inmbolmie/elfacun/images/B1.JPG

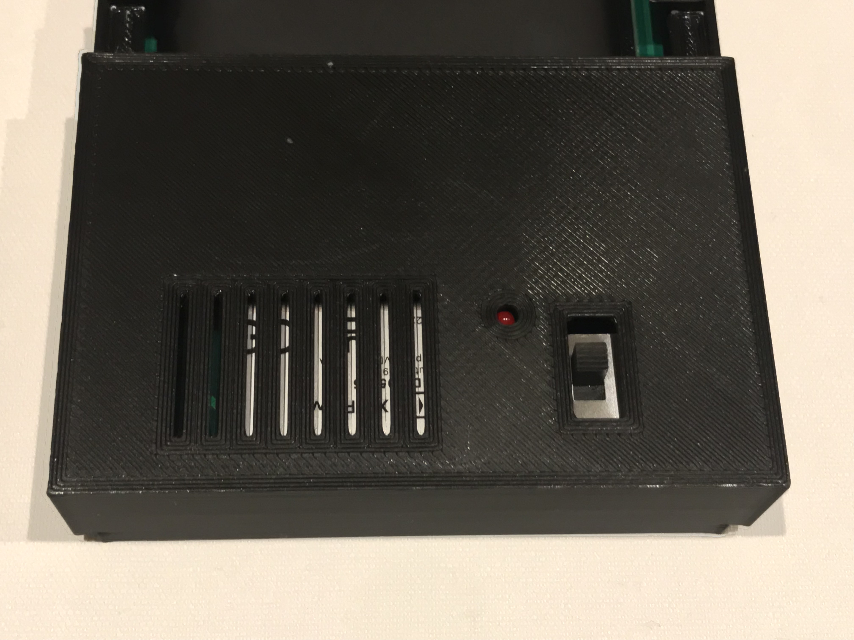
images/B1.JPG
