inmbolmie/elfacun/images/buttons.jpeg

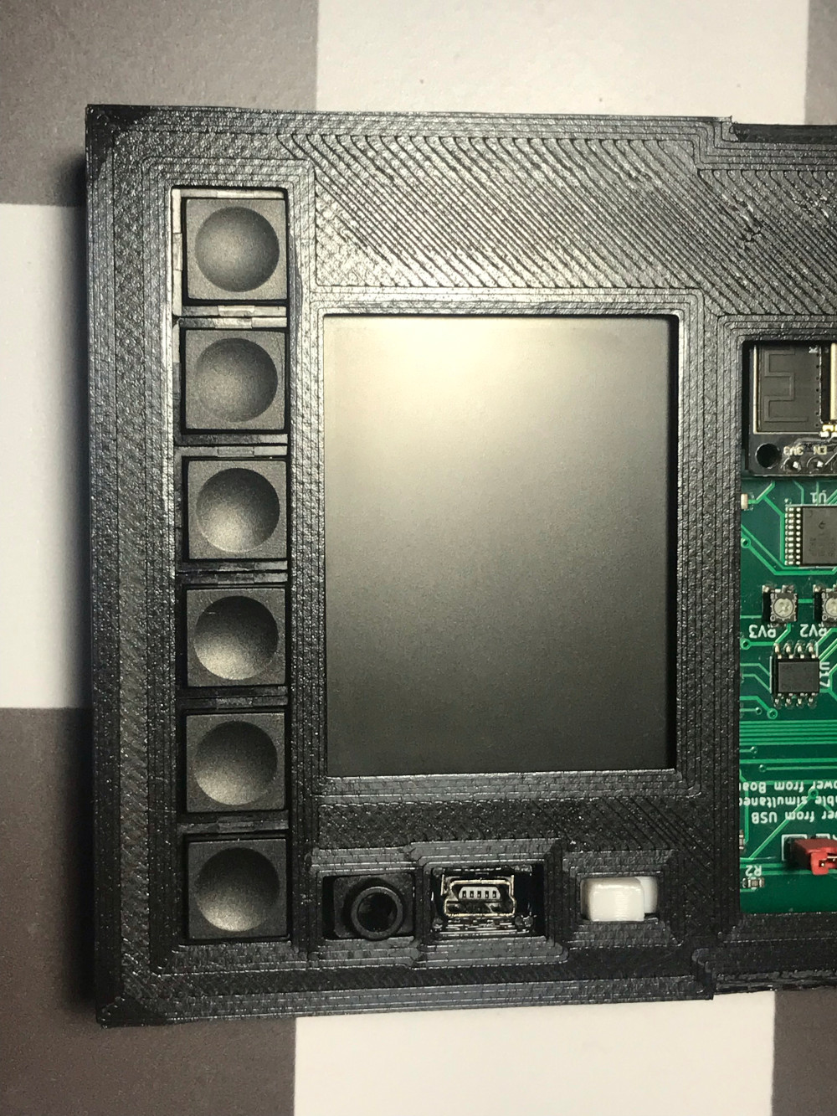
images/buttons.jpeg
