inmbolmie/elfacun/images/R6.jpg

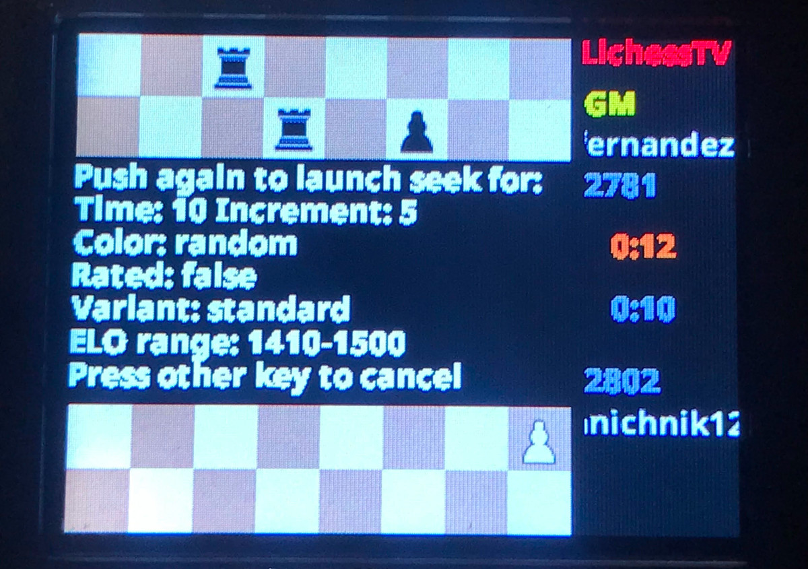
images/R6.jpg
