inmbolmie/elfacun/Kicad/v2.1/elfacun_v21.png

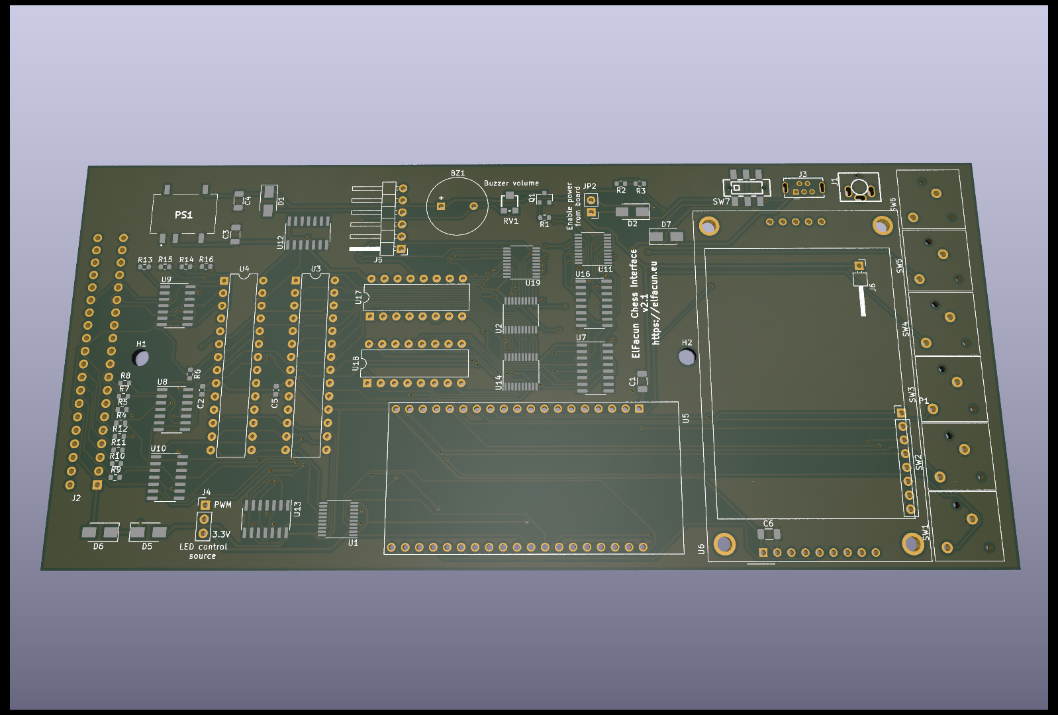
Kicad/v2.1/elfacun_v21.png
