inmbolmie/elfacun/pcb/v2.1/sample.png

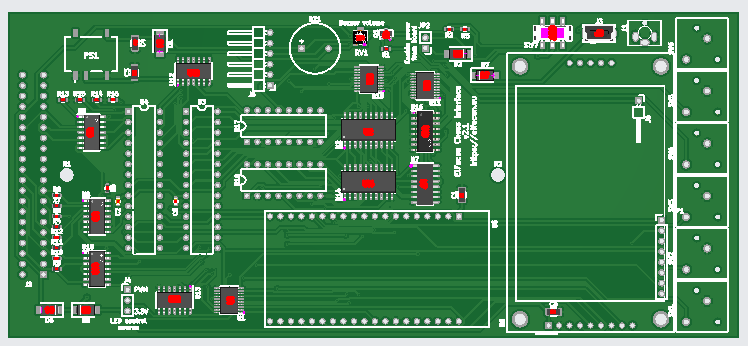
pcb/v2.1/sample.png
