inmbolmie/elfacun/elfacun/screen.cpp

/*
    ElFacun Chess Module software for ESP32
    © 2022 Inmbolmie inmbolmie [at] gmail [dot] com
    Distributed under the GNU GPL V3.0 license

    This program is distributed WITHOUT ANY WARRANTY, even the
    implied warranty of MERCHANTABILITY or FITNESS FOR A PARTICULAR
    PURPOSE.  See the GNU General Public License for more details.
*/

#include "screen.h"
#include "serial.h"
#include "i2c_clock.h"
#include "lichess.h"
#include "driver/ledc.h"

int lichessTopLastShownTime = 0;
int lichessBottomLastShownTime = 0;
boolean lichessBottomLastShownTimeToMove = false;
boolean lichessTopLastShownTimeToMove = false;
boolean centerBoardOnScreen = true;

char lichessConfirmationMsg[200];
boolean displayLichessConfirmationMsg = false;
boolean displayLichessSeekMsg = false;
const char*  lichessBottomNameActive;
const char*  lichessTopNameActive;
boolean signalResetTopPlayer = false;
boolean signalResetBottomPlayer = false;
int topPlayerTextSize = 0;
int bottomPlayerTextSize = 0;

int lastLedShownScreen = 64;

int lastRssiPainted = 0;

unsigned long lastLedShownScreenMillis = 0;

boolean doPaintBLEConnectedIcon = false;
boolean doPaintBLEConnectedIconDisabled = false;
boolean doClearBLEConnectedIcon = false;

boolean doPaintChess960ModeIcon = false;
boolean doClearChess960ModeIcon = false;

int toScrollTopPlayer = 0;
int toScrollBottomPlayer = 0;

byte currentTftBrightness = 255;

boolean isBrightnessAdjustmentDisabled = true;

SemaphoreHandle_t xScreenSemaphore;

const TickType_t screenSemaphoreTimeout = 5000 / portTICK_PERIOD_MS;

TFT_eSPI tft = TFT_eSPI();
TFT_eSprite spr = TFT_eSprite(&tft);
TFT_eSprite sprb = TFT_eSprite(&tft);


void initialize_tft() {
  tft.init();            // initialize LCD
  tft.setRotation(3);    //3-Landscape mode with SD card slot pointing backwards
  tft.setSwapBytes(true);
  tft.fillScreen(TFT_BLACK);
  tft.setCursor(0, 0);
  tft.setTextColor(TFT_WHITE); tft.setTextSize(1);

  //Semaphore to handle access to screen and SPI bus
  xScreenSemaphore = xSemaphoreCreateMutex();
  //unlocked by default
  xSemaphoreGive( ( xScreenSemaphore ) );

}




void paintBLEDebugUpdateMode() {

  //Called from displayBoard so no lock needed
  tft.fillRect(280, 220, 20, 20, TFT_BLACK);
  tft.setTextSize(1);
  tft.setTextWrap(false);

  tft.setCursor(280, 220);
  tft.setTextColor(TFT_WHITE);
  tft.printf("%d" , updateModeTypeBUSBBoard);

  return;
}



void paintBLEConnectedIcon() {
  //Called from displayBoard so no lock needed
  tft.fillRect(300, 220, 20, 20, TFT_BLACK);
  tft.setTextSize(1);
  tft.setTextWrap(false);

  tft.setCursor(300, 220);
  tft.setTextColor(TFT_WHITE);
  tft.printf("B");
  return;
}


void paintChess960ModeIcon() {
  //Called from displayBoard so no lock needed
  tft.fillRect(250, 220, 20, 20, TFT_BLACK);
  tft.setTextSize(1);
  tft.setTextWrap(false);

  tft.setCursor(250, 220);
  tft.setTextColor(TFT_WHITE);
  tft.printf("960");
  return;
}



void paintBLEConnectedIconDisabled() {

  //Called from displayBoard so no lock needed
  paintBLEConnectedIcon();
  tft.drawLine(298, 218, 313, 233, TFT_WHITE);
  tft.drawLine(313, 218, 298, 233, TFT_WHITE);

  return;
}

void paintBLEConnectedIconClear() {
  //Called from displayBoard so no lock needed

  tft.fillRect(298, 218, 20, 20, TFT_BLACK);
  return;
}

void paintChess960ModeIconClear() {
  //Called from displayBoard so no lock needed

  tft.fillRect(248, 218, 30, 20, TFT_BLACK);
  return;
}



void clearScreen() {
  xSemaphoreTake( xScreenSemaphore, ( TickType_t ) screenSemaphoreTimeout );
  tft.fillScreen(TFT_BLACK);
  if (BLEdeviceConnected) {
    paintBLEConnectedIcon();
  }
  if (chess960ModeEnabled) {
    paintChess960ModeIcon();
  }

  xSemaphoreGive( ( xScreenSemaphore ) );
}


void greyScreen() {
  xSemaphoreTake( xScreenSemaphore, ( TickType_t ) screenSemaphoreTimeout );
  tft.fillScreen(TFT_DARKGREY);
  if (BLEdeviceConnected) {
    paintBLEConnectedIcon();
  }
  if (chess960ModeEnabled) {
    paintChess960ModeIcon();
  }


  xSemaphoreGive( ( xScreenSemaphore ) );
}


void setDefaultTftBrightness() {
  currentTftBrightness = (uint8_t)atoi(screenBrightnessDefault);

  if (currentTftBrightness < 5) {
    currentTftBrightness = 64;
  }
  if (serialLog) Serial.print("Set default brightness: ");
  if (serialLog) Serial.println(currentTftBrightness, DEC);
  setTftBrightness(currentTftBrightness);
}

void setTftBrightness(byte brightness) {

  if (!isBrightnessAdjustmentDisabled) {

    if (serialLog) Serial.print("Set brightness: ");
    if (serialLog) Serial.println(brightness, DEC);
    //Set brightness on V2 hardware
    if (isV2Hardware) {
      ledcSetup(5, 800000, 8);
      ledcAttachPin(SCREEN_BRIGHTNESS, 5);
      ledcWrite(5, brightness);
    }
    currentTftBrightness = brightness;
  } else {

    if (serialLog) Serial.println("Set brightness MAX");
    pinMode(SCREEN_BRIGHTNESS, OUTPUT);
    digitalWrite(SCREEN_BRIGHTNESS, true);
  }

}


void increaseTftBrightness() {

  if (currentTftBrightness <= 252) {
    currentTftBrightness += 2;
  } else {
    currentTftBrightness = 255;
  }

  setTftBrightness(currentTftBrightness);
}


void decreaseTftBrightness() {

  if (currentTftBrightness >= 7) {
    currentTftBrightness -= 2;
  } else {
    currentTftBrightness = 5;
  }

  setTftBrightness(currentTftBrightness);

}


void storeAdjustedBrightness() {

  char cstr[4];
  sprintf(cstr, "%d", currentTftBrightness);
  storeNvsValue("screenbr", cstr);

}



// These read 16- and 32-bit types from the SD card file.
// BMP data is stored little-endian, Arduino is little-endian too.
// May need to reverse subscript order if porting elsewhere.

uint16_t read16(fs::File &f) {
  uint16_t result;
  ((uint8_t *)&result)[0] = f.read(); // LSB
  ((uint8_t *)&result)[1] = f.read(); // MSB
  return result;
}

uint32_t read32(fs::File &f) {
  uint32_t result;
  ((uint8_t *)&result)[0] = f.read(); // LSB
  ((uint8_t *)&result)[1] = f.read();
  ((uint8_t *)&result)[2] = f.read();
  ((uint8_t *)&result)[3] = f.read(); // MSB
  return result;
}


// Bodmers BMP image rendering function
// https://github.com/Bodmer/TFT_eSPI/blob/master/examples/Generic/TFT_SPIFFS_BMP/BMP_functions.ino
void drawBmp(const char *filename, int16_t x, int16_t y) {

  if ((x >= tft.width()) || (y >= tft.height())) return;

  fs::File bmpFS;

  // Open requested file on SD card
  bmpFS = SPIFFS.open(filename, "r");

  if (!bmpFS)
  {
    if (serialLog) Serial.print("File not found: ");
    if (serialLog) Serial.println(filename);
    return;
  }

  uint32_t seekOffset;
  uint16_t w, h, row, col;
  uint8_t  r, g, b;

  uint32_t startTime = millis();

  if (read16(bmpFS) == 0x4D42)
  {
    read32(bmpFS);
    read32(bmpFS);
    seekOffset = read32(bmpFS);
    read32(bmpFS);
    w = read32(bmpFS);
    h = read32(bmpFS);

    if ((read16(bmpFS) == 1) && (read16(bmpFS) == 24) && (read32(bmpFS) == 0))
    {
      y += h - 1;

      bool oldSwapBytes = tft.getSwapBytes();
      tft.setSwapBytes(true);
      bmpFS.seek(seekOffset);

      uint16_t padding = (4 - ((w * 3) & 3)) & 3;
      uint8_t lineBuffer[w * 3 + padding];

      for (row = 0; row < h; row++) {

        bmpFS.read(lineBuffer, sizeof(lineBuffer));
        uint8_t*  bptr = lineBuffer;
        uint16_t* tptr = (uint16_t*)lineBuffer;
        // Convert 24 to 16 bit colours
        for (uint16_t col = 0; col < w; col++)
        {
          b = *bptr++;
          g = *bptr++;
          r = *bptr++;
          *tptr++ = ((r & 0xF8) << 8) | ((g & 0xFC) << 3) | (b >> 3);
        }

        // Push the pixel row to screen, pushImage will crop the line if needed
        // y is decremented as the BMP image is drawn bottom up
        tft.pushImage(x, y--, w, 1, (uint16_t*)lineBuffer);
      }
      tft.setSwapBytes(oldSwapBytes);
      //if (serialLog) Serial.print("Loaded in ");
      //if (serialLog) Serial.print(millis() - startTime);
      //if (serialLog) Serial.println(" ms");
    }
    else if (serialLog) Serial.println("BMP format not recognized.");
  }
  bmpFS.close();
}


//
//void displayLichessConfirmationMessage() {
//
//  if (displayLichessConfirmationMsg) {
//    spr.pushSprite(0, 60);
//    if (serialLog) Serial.println("Push sprite------------------------------------>");
//  }
//}



const char hex[17] = "0123456789ABCDEF";

void displayBoard() {
  xSemaphoreTake( xScreenSemaphore, ( TickType_t ) screenSemaphoreTimeout );

  int boardOriginX = 0;
  int boardOriginY = 0;

  if ((isExternalClock || centerBoardOnScreen) && !isLichessConnected) {
    boardOriginX = 40;
    boardOriginY = 0;
  }

  tft.setTextSize(2);
  tft.setCursor(boardOriginX, boardOriginY);



  int square = 0;
  int visibleSquare = 0;
  int line = 0;
  int linepos = 0;

  int x = boardOriginX;
  int y = boardOriginY;

  if (!isExternalClock && refreshClock) {
    //Release temporarily to call display_clock()
    xSemaphoreGive( ( xScreenSemaphore ) );
    display_clock();
    xSemaphoreTake( xScreenSemaphore, ( TickType_t ) screenSemaphoreTimeout );
    send_clock();
    refreshClock = false;
  }

  boolean ledActivatedScreen = false;

  while (square < 64) {

    visibleSquare = square;

    byte bgcolor = 1;
    if ((line % 2) == (square % 2)) {
      bgcolor = 0;
    }

    x = boardOriginX + (square % 8) * 30;
    y = boardOriginY + line * 30;

    byte squareToShow = currentPos[visibleSquare];

    if (boardInverted) {
      squareToShow = currentPos[63 - visibleSquare];
    }

    if (isLichessConnected) {
      int index = visibleSquare;
      if (boardInverted) {
        index = 63 - visibleSquare;
      }
      squareToShow = lichessBoardPosition[index];
      if (lichessBoardPositionMarked[index] == 1) {
        bgcolor += 2;
      }

      //RSSI indicator
      if (measuredRssi != lastRssiPainted) {
        if (measuredRssi == 1) {
          tft.fillCircle(250, 230, 6, TFT_GREEN);
        }
        if (measuredRssi == 2) {
          tft.fillCircle(250, 230, 6, TFT_ORANGE);
        }
        if (measuredRssi == 3) {
          tft.fillCircle(250, 230, 6, TFT_RED);
        }
      }
    }

    if (isPassiveMode && !updateRemoteLedsAvailable()) {

      int index = visibleSquare;

      if ((lastLedShownScreenMillis + 500) < millis() ) {

        if (lastLedShownScreen == 64 || index > lastLedShownScreen ) {

          if (ledStatus[63 - index] && index != lastLedShownScreen && !ledActivatedScreen) {
            bgcolor += 2;
            lastLedShownScreen = index;
            lastLedShownScreenMillis = millis();
            ledActivatedScreen = true;
            buup();
          }
        }
      } else if (index == lastLedShownScreen) {
        bgcolor += 2;
        ledActivatedScreen = true;
      }
    }


    if ((lastDrawn[visibleSquare] != squareToShow || lastDrawnBG[visibleSquare] != bgcolor)  && ((displayLichessConfirmationMsg == false && displayLichessSeekMsg == false) || square <= 15 || square >= 48  )) {
      lastDrawn[visibleSquare] = squareToShow;
      lastDrawnBG[visibleSquare] = bgcolor;
      String pieceChar = String(squareToShow, HEX);
      pieceChar.toUpperCase();
      String filename = "/" + pieceChar + bgcolor + ".bmp";
      drawBmp(filename.c_str(), x, y);


    }

    square++;
    linepos++;
    if (linepos == 8) {
      linepos = 0;
      line++;
      tft.println("");
    }
  }


  if (!ledActivatedScreen) {
    lastLedShownScreen = 64;
  }

  //displayLichessConfirmationMessage();

  //paintBLEDebugUpdateMode();

  if (doPaintBLEConnectedIcon) {
    if (serialLog) Serial.println("Paint connected BLE");
    doPaintBLEConnectedIcon = false;
    paintBLEConnectedIcon();
  }

  if (doPaintBLEConnectedIconDisabled) {
    if (serialLog) Serial.println("Paint disabled BLE");
    doPaintBLEConnectedIconDisabled = false;
    paintBLEConnectedIconDisabled();
  }

  if (doClearBLEConnectedIcon) {
    if (serialLog) Serial.println("Clear BLE");
    doClearBLEConnectedIcon = false;
    paintBLEConnectedIconClear();
  }

  if (doPaintChess960ModeIcon) {
    if (serialLog) Serial.println("Paint 960");
    doPaintChess960ModeIcon = false;
    paintChess960ModeIcon();
  }


  if (doClearChess960ModeIcon) {
    if (serialLog) Serial.println("Clear 960");
    doClearChess960ModeIcon = false;
    paintChess960ModeIconClear();
  }


  xSemaphoreGive( ( xScreenSemaphore ) );


}






// http://javl.github.io/image2cpp/
// 'Scally', 107x180px
const uint16_t epd_bitmap_scally [] PROGMEM = {
  0x0000, 0x0000, 0x0000, 0x0000, 0x0000, 0x0000, 0x0000, 0x0000, 0x0000, 0x0000, 0x0000, 0x0000, 0x0000, 0x0000, 0x0000, 0x0000, 
  0x0000, 0x0000, 0x0000, 0x0000, 0x0000, 0x0000, 0x0000, 0x0000, 0x0000, 0x0000, 0x0000, 0x0000, 0x0000, 0x0000, 0x0000, 0x0000, 
  0x0000, 0x0000, 0x0000, 0x0000, 0x0000, 0x0000, 0x0000, 0x0000, 0x1082, 0x2104, 0x31a6, 0x4a69, 0x5acb, 0x6b6d, 0x7bcf, 0x7bcf, 
  0x7bcf, 0x7bcf, 0x7bcf, 0x7bcf, 0x7bcf, 0x73ae, 0x630c, 0x5acb, 0x52aa, 0x4208, 0x2965, 0x18c3, 0x0861, 0x0000, 0x0000, 0x0000, 
  0x0000, 0x0000, 0x0000, 0x0000, 0x0000, 0x0000, 0x0000, 0x0000, 0x0000, 0x0000, 0x0000, 0x0000, 0x0000, 0x0000, 0x0000, 0x0000, 
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
  0x9492, 0x9cd3, 0x9cf3, 0x9cf3, 0x9cf3, 0x9cf3, 0x9cf3, 0x9cf3, 0x9cf3, 0x9cd3, 0x94b2, 0x9492, 0x9492, 0x9492, 0x94b2, 0x94b2, 
  0x94b2, 0x94b2, 0x94b2, 0x9492, 0x9492, 0x9492, 0x94b2, 0x9492, 0x94b2, 0x94b2, 0x94b2, 0x8c71, 0x8410, 0x632c, 0x39c7, 0x0841, 
  0x0000, 0x0000, 0x0000, 0x0000, 0x0000, 0x0000, 0x0000, 0x0000, 0x0000, 0x0000, 0x0000, 0x0000, 0x0000, 0x0000, 0x0000, 0x0000, 
  0x0000, 0x0000, 0x0000, 0x0000, 0x0000, 0x0000, 0x0000, 0x0000, 0x0000, 0x0000, 0x0000, 0x0000, 0x0000, 0x0000, 0x0000, 0x0000, 
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
};




void displayScallyHomage() {

  if (strcmp(scallyHomage, "TRUE") == 0) {
    
    tft.pushImage(106, 10, 107, 180, epd_bitmap_scally);
    tft.setTextSize(1);
    tft.setCursor(60, 210);
    tft.setTextColor(TFT_DARKGREY);
    tft.print("In memoriam Alan 'Scally' Cooper");
    tft.setCursor(130, 225);
    tft.print("1956-2024");
    delay(1500);
  }
  
}


void displayLichessLogo() {
  xSemaphoreTake( xScreenSemaphore, ( TickType_t ) screenSemaphoreTimeout );
  if (serialLog) Serial.println("Displaying Lichess logo");
  tft.fillScreen(TFT_BLACK);
  displayScallyHomage();
  tft.fillScreen(TFT_BLACK);
  drawBmp("/lich.bmp", 110, 70);
  xSemaphoreGive( ( xScreenSemaphore ) );
}


void displayModeALogo() {
  xSemaphoreTake( xScreenSemaphore, ( TickType_t ) screenSemaphoreTimeout );
  if (serialLog) Serial.println("Displaying Mode A logo");
  tft.fillScreen(TFT_BLACK);
  displayScallyHomage();
  tft.fillScreen(TFT_BLACK);
  drawBmp("/modea.bmp", 110, 100);
  xSemaphoreGive( ( xScreenSemaphore ) );
}


void displayModeBLogo() {
  xSemaphoreTake( xScreenSemaphore, ( TickType_t ) screenSemaphoreTimeout );
  if (serialLog) Serial.println("Displaying Mode B logo");
  tft.fillScreen(TFT_BLACK);
  displayScallyHomage();
  tft.fillScreen(TFT_BLACK);
  drawBmp("/modeb.bmp", 110, 100);
  xSemaphoreGive( ( xScreenSemaphore ) );
}

//http://javl.github.io/image2cpp/
const uint16_t epd_bitmap_modec [] PROGMEM = {
  0x0000, 0x0000, 0x0000, 0x0000, 0x0000, 0x0000, 0x0000, 0x0000, 0x0000, 0x0000, 0x0000, 0x0000, 0x0000, 0x0000, 0x0000, 0x0000,
  0x0000, 0x0000, 0x0000, 0x0000, 0x0000, 0x0000, 0x0000, 0x0000, 0x0000, 0x0000, 0x0000, 0x0000, 0x0000, 0x0000, 0x0000, 0x0000,
  0x0000, 0x0000, 0x0000, 0x0000, 0x0000, 0x0000, 0x0000, 0x0000, 0x0000, 0x0000, 0x0000, 0x0000, 0x0000, 0x0000, 0x0000, 0x0000,
  0x0000, 0x0000, 0x0000, 0x0000, 0x0000, 0x0000, 0x0000, 0x0000, 0x0000, 0x0000, 0x0000, 0x0000, 0x0000, 0x0000, 0x0000, 0x0000,
  0x0000, 0x0000, 0x0000, 0x0000, 0x0000, 0x0000, 0x0000, 0x0000, 0x0000, 0x0000, 0x0000, 0x0000, 0x0000, 0x0000, 0x0000, 0x0000,
  0x0000, 0x0000, 0x0000, 0x0000, 0x0000, 0x0000, 0x0000, 0x0000, 0x39c7, 0xffdf, 0xffdf, 0xffdf, 0xd6ba, 0x0000, 0x0000, 0x0000,
  0x0000, 0x0000, 0x0000, 0x0000, 0x18e3, 0xef5d, 0xffdf, 0xffdf, 0xf7be, 0x10a2, 0x0000, 0x0000, 0x0000, 0x0000, 0x0000, 0x0000,
  0x0000, 0x0000, 0x0000, 0x0000, 0x0000, 0x0000, 0x0000, 0x0000, 0x0000, 0x0000, 0x0000, 0x0000, 0x0000, 0x0000, 0x0000, 0x0000,
  0x0000, 0x0000, 0x0000, 0x0000, 0x0000, 0x0000, 0xf79e, 0xffdf, 0x8430, 0x0000, 0x0000, 0x0000, 0x0000, 0x0000, 0x0000, 0x0000,
  0x0000, 0x0000, 0x0000, 0x0000, 0x0000, 0x0000, 0x0000, 0x0000, 0x0000, 0x0000, 0x0000, 0x0000, 0x0000, 0x10a2, 0x9492, 0xce59,
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
  //drawBmp("/modec.bmp", 118, 110);
  xSemaphoreGive( ( xScreenSemaphore ) );
}





void clear_message() {
  xSemaphoreTake( xScreenSemaphore, ( TickType_t ) screenSemaphoreTimeout );
  tft.fillRect(245, 110, 75, 30, TFT_BLACK);
  xSemaphoreGive( ( xScreenSemaphore ) );
}


void display_message(String message) {
  xSemaphoreTake( xScreenSemaphore, ( TickType_t ) screenSemaphoreTimeout );
  tft.fillRect(245, 115, 75, 30, TFT_BLACK);
  tft.setCursor(245, 115);
  tft.setTextColor(TFT_WHITE);
  tft.println(message);
  xSemaphoreGive( ( xScreenSemaphore ) );

}


void display_clock() {
  xSemaphoreTake( xScreenSemaphore, ( TickType_t ) screenSemaphoreTimeout );


  if (!boardInverted) {

    tft.fillRect(245, 30, 75, 50, TFT_BLACK);
    tft.setCursor(255, 50);
    tft.setTextColor(TFT_WHITE);
    tft.printf("%01d", rhours);
    tft.print(":");
    tft.printf("%02d", rmins);
    tft.print(".");
    tft.printf("%02d", rsecs);

    tft.fillRect(245, 180, 75, 30, TFT_BLACK);
    tft.setCursor(255, 180);
    tft.printf("%01d", lhours);
    tft.print(":");
    tft.printf("%02d", lmins);
    tft.print(".");
    tft.printf("%02d", lsecs);
  } else {

    tft.fillRect(245, 30, 75, 50, TFT_BLACK);
    tft.setCursor(255, 50);
    tft.setTextColor(TFT_WHITE);
    tft.printf("%01d", lhours);
    tft.print(":");
    tft.printf("%02d", lmins);
    tft.print(".");
    tft.printf("%02d", lsecs);

    tft.fillRect(245, 180, 75, 30, TFT_BLACK);
    tft.setCursor(255, 180);
    tft.printf("%01d", rhours);
    tft.print(":");
    tft.printf("%02d", rmins);
    tft.print(".");
    tft.printf("%02d", rsecs);
  }

  xSemaphoreGive( ( xScreenSemaphore ) );
}



void paintLichessPlayerTopSprite(const char* lichessTopTitle, const char*  lichessTopName, long  lichessTopRating) {
  xSemaphoreTake( xScreenSemaphore, ( TickType_t ) screenSemaphoreTimeout );

  tft.fillRect(240, 0, 80, 80, TFT_BLACK);
  tft.setTextSize(1);
  tft.setTextWrap(false);

  if (isLichessConnected && !isLichessGameActive()) {
    tft.setCursor(245, 0);
    tft.setTextColor(TFT_RED);
    tft.printf("LichessTV");
  }

  tft.setCursor(247, 25);
  tft.setTextColor(TFT_ORANGE);
  tft.printf("%s", lichessTopTitle);


  //tft.setCursor(247, 45);
  //tft.setTextColor(TFT_WHITE);
  //tft.printf("%s", lichessTopName);


  if (lichessTopRating != NULL) {
    tft.setCursor(247, 65);
    tft.setTextColor(TFT_DARKGREY);
    tft.printf("%d", lichessTopRating);
  }



  spr.setColorDepth(8);
  spr.deleteSprite();
  spr.loadFont("NotoSansBold15"); // Must load the font first into the sprite class
  topPlayerTextSize = spr.textWidth(lichessTopName) + 7;
  spr.createSprite(topPlayerTextSize, 17);
  //spr.fillSprite(TFT_RED);

  spr.setTextColor(TFT_WHITE, TFT_BLACK); // Set the sprite font colour and the background colour
  //tft.setCursor(247, 45);
  //spr.setScrollRect(0, 0, 10 * strlen(lichessTopName), 17, TFT_BLACK);
  spr.printToSprite(lichessTopName);    // Prints to tft cursor position, tft cursor NOT moved

  spr.unloadFont(); // Remove the font from sprite class to recover memory used
  tft.fillRect(247, 45, 80, 20, TFT_BLACK);
  spr.pushSprite(247, 45);
  if (serialLog) Serial.print("Sprite TOP width----------------------> ");
  if (serialLog) Serial.println(topPlayerTextSize, DEC);


  toScrollTopPlayer = topPlayerTextSize + 60;
  delete lichessTopNameActive;
  lichessTopNameActive = strdup(lichessTopName);

  signalResetTopPlayer = false;

  xSemaphoreGive( ( xScreenSemaphore ) );
  return;

}


void refreshLichessPlayerTopSprite() {
  xSemaphoreTake( xScreenSemaphore, ( TickType_t ) screenSemaphoreTimeout );

  if (spr.width() > 0) {

    toScrollTopPlayer--;

    if ((toScrollTopPlayer >= 80) && (toScrollTopPlayer <= topPlayerTextSize) ) {
      spr.scroll(-1);
      spr.pushSprite(247, 45);
    }

    if (toScrollTopPlayer < 20) {
      signalResetTopPlayer = true;
    }

    if (toScrollTopPlayer < 20 && signalResetBottomPlayer) {
      signalResetBottomPlayer = false;
      spr.deleteSprite();
      spr.createSprite(topPlayerTextSize, 17);
      spr.loadFont("NotoSansBold15");
      //tft.fillRect(247, 45, 80, 20, TFT_BLACK);
      spr.fillSprite(TFT_BLACK);
      tft.setCursor(247, 45);
      spr.printToSprite(lichessTopNameActive);
      toScrollTopPlayer = topPlayerTextSize + 60;
      spr.unloadFont();
      spr.pushSprite(247, 45);

    }
  }

  xSemaphoreGive( ( xScreenSemaphore ) );
}



void paintLichessPlayerBottomSprite(const char* lichessBottomTitle, const char*  lichessBottomName, long  lichessBottomRating) {
  xSemaphoreTake( xScreenSemaphore, ( TickType_t ) screenSemaphoreTimeout );


  tft.fillRect(240, 120, 80, 80, TFT_BLACK);
  tft.setTextSize(1);
  tft.setTextWrap(false);

  if (lichessBottomRating != NULL) {
    tft.setCursor(247, 160);
    tft.setTextColor(TFT_DARKGREY);
    tft.printf("%d", lichessBottomRating);
  }

  //tft.setCursor(247, 180);
  //tft.setTextColor(TFT_WHITE);
  //tft.printf("%s", lichessBottomName);


  tft.setCursor(247, 200);
  tft.setTextColor(TFT_ORANGE);
  tft.printf("%s", lichessBottomTitle);


  sprb.setColorDepth(8);
  sprb.deleteSprite();
  sprb.loadFont("NotoSansBold15"); // Must load the font first into the sprite class
  bottomPlayerTextSize = sprb.textWidth(lichessBottomName) + 7;
  sprb.createSprite(bottomPlayerTextSize, 17);
  //spr.fillSprite(TFT_RED);

  sprb.setTextColor(TFT_WHITE, TFT_BLACK); // Set the sprite font colour and the background colour
  //tft.setCursor(247, 45);
  //spr.setScrollRect(0, 0, 10 * strlen(lichessTopName), 17, TFT_BLACK);
  sprb.printToSprite(lichessBottomName);    // Prints to tft cursor position, tft cursor NOT moved

  sprb.unloadFont(); // Remove the font from sprite class to recover memory used
  tft.fillRect(247, 180, 80, 20, TFT_BLACK);
  sprb.pushSprite(247, 180);

  if (serialLog) Serial.print("Sprite BOTTOM width----------------------> ");
  if (serialLog) Serial.println(bottomPlayerTextSize, DEC);

  toScrollBottomPlayer = bottomPlayerTextSize + 60;
  delete lichessBottomNameActive;
  lichessBottomNameActive = strdup(lichessBottomName);

  signalResetBottomPlayer = false;

  xSemaphoreGive( ( xScreenSemaphore ) );
  return;
}



void refreshLichessPlayerBottomSprite() {
  xSemaphoreTake( xScreenSemaphore, ( TickType_t ) screenSemaphoreTimeout );

  if (sprb.width() > 0) {

    toScrollBottomPlayer--;

    if ((toScrollBottomPlayer >= 80) && (toScrollBottomPlayer <= bottomPlayerTextSize )) {
      sprb.scroll(-1);
      sprb.pushSprite(247, 180);
    }

    if (toScrollBottomPlayer < 20) {
      signalResetBottomPlayer = true;
    }

    if (toScrollBottomPlayer < 20 && signalResetTopPlayer) {
      signalResetTopPlayer = false;
      sprb.deleteSprite();
      sprb.createSprite(bottomPlayerTextSize, 17);
      sprb.loadFont("NotoSansBold15");
      //tft.fillRect(247, 180, 80, 20, TFT_BLACK);
      sprb.fillSprite(TFT_BLACK);
      tft.setCursor(247, 180);
      sprb.printToSprite(lichessBottomNameActive);
      toScrollBottomPlayer = bottomPlayerTextSize + 60;
      sprb.unloadFont();
      sprb.pushSprite(247, 180);

    }
  }

  xSemaphoreGive( ( xScreenSemaphore ) );
}




void paintLichessPlayerTop(const char* lichessTopTitle, const char*  lichessTopName, long  lichessTopRating) {
  xSemaphoreTake( xScreenSemaphore, ( TickType_t ) screenSemaphoreTimeout );

  tft.fillRect(240, 0, 80, 80, TFT_BLACK);
  tft.setTextSize(1);
  tft.setTextWrap(false);

  if (isLichessConnected && !isLichessGameActive()) {
    tft.setCursor(245, 0);
    tft.setTextColor(TFT_RED);
    tft.printf("LichessTV");
  }

  tft.setCursor(247, 25);
  tft.setTextColor(TFT_ORANGE);
  tft.printf("%s", lichessTopTitle);


  tft.setCursor(247, 45);
  tft.setTextColor(TFT_WHITE);
  tft.printf("%s", lichessTopName);


  if (lichessTopRating != NULL) {
    tft.setCursor(247, 65);
    tft.setTextColor(TFT_DARKGREY);
    tft.printf("%d", lichessTopRating);
  }

  xSemaphoreGive( ( xScreenSemaphore ) );

  return;
}

void paintLichessPlayerBottom(const char* lichessBottomTitle, const char*  lichessBottomName, long  lichessBottomRating) {
  xSemaphoreTake( xScreenSemaphore, ( TickType_t ) screenSemaphoreTimeout );


  tft.fillRect(240, 120, 80, 80, TFT_BLACK);
  tft.setTextSize(1);
  tft.setTextWrap(false);

  if (lichessBottomRating != NULL) {
    tft.setCursor(247, 160);
    tft.setTextColor(TFT_DARKGREY);
    tft.printf("%d", lichessBottomRating);
  }

  tft.setCursor(247, 180);
  tft.setTextColor(TFT_WHITE);
  tft.printf("%s", lichessBottomName);


  tft.setCursor(247, 200);
  tft.setTextColor(TFT_ORANGE);
  tft.printf("%s", lichessBottomTitle);


  xSemaphoreGive( ( xScreenSemaphore ) );
  return;
}

void paintLichessPlayerClear() {
  xSemaphoreTake( xScreenSemaphore, ( TickType_t ) screenSemaphoreTimeout );
  tft.fillRect(240, 0, 80, 240, TFT_BLACK);
  lichessTopLastShownTime = 0;
  lichessBottomLastShownTime = 0;
  xSemaphoreGive( ( xScreenSemaphore ) );
  return;
}

void paintLichessTimeTop(long lichessTopTime, boolean isTimeToMove) {
  xSemaphoreTake( xScreenSemaphore, ( TickType_t ) screenSemaphoreTimeout );


  if (lichessTopTime != NULL) {

    if (lichessTopTime / 1000 == lichessTopLastShownTime && isTimeToMove == lichessTopLastShownTimeToMove) {
      xSemaphoreGive( ( xScreenSemaphore ) );
      return;
    }

    lichessTopLastShownTime = lichessTopTime / 1000;
    lichessTopLastShownTimeToMove = isTimeToMove;

    long minutes = lichessTopTime / 60000;
    long seconds = (lichessTopTime / 1000) % 60;

    tft.fillRect(247, 95, 80, 20, TFT_BLACK);

    tft.setCursor(260, 95);
    if (!isTimeToMove) {
      tft.setTextColor(TFT_DARKGREY);
    } else {
      tft.setTextColor(0xFA80);
    }
    tft.printf("%d:%02d", minutes, seconds);
  }
  xSemaphoreGive( ( xScreenSemaphore ) );
  return;
}

void paintLichessTimeBottom(long lichessBottomTime, boolean isTimeToMove) {
  xSemaphoreTake( xScreenSemaphore, ( TickType_t ) screenSemaphoreTimeout );
  if (lichessBottomTime != NULL) {

    if (lichessBottomTime / 1000 == lichessBottomLastShownTime && isTimeToMove == lichessBottomLastShownTimeToMove) {
      xSemaphoreGive( ( xScreenSemaphore ) );
      return;
    }

    lichessBottomLastShownTime = lichessBottomTime / 1000;
    lichessBottomLastShownTimeToMove = isTimeToMove;

    long minutes = lichessBottomTime / 60000;
    long seconds = (lichessBottomTime / 1000) % 60;

    tft.fillRect(247, 125, 80, 20, TFT_BLACK);

    tft.setCursor(260, 125);
    if (!isTimeToMove) {
      tft.setTextColor(TFT_DARKGREY);
    } else {
      tft.setTextColor(0xFA80);
    }
    tft.printf("%d:%02d", minutes, seconds);
  }
  xSemaphoreGive( ( xScreenSemaphore ) );
  return;

}


void askForLichessConfirmation(const char* lichessTime, const char* lichessIncrement, const char* lichessRated, const char* lichessColor, const char* lichessElo) {

  //Called from the button read code so the semaphore is already taken

  displayLichessConfirmationMsg = true;

  //spr.setColorDepth(8);
  //spr.createSprite(240, 120);
  //spr.fillSprite(TFT_RED);
  //spr.loadFont("NotoSansBold15"); // Must load the font first into the sprite class
  //spr.setTextColor(TFT_WHITE, TFT_BLACK); // Set the sprite font colour and the background colour
  //tft.setCursor(0,0);
  //spr.setScrollRect(0, 0, 200, 80, TFT_YELLOW);
  //spr.printToSprite(lichessConfirmationMsg);    // Prints to tft cursor position, tft cursor NOT moved
  //spr.unloadFont(); // Remove the font from sprite class to recover memory used

  tft.fillRect(0, 60, 240, 120, TFT_BLACK);
  tft.setCursor(0, 63);
  tft.setTextColor(TFT_WHITE);
  if (strcmp(lichessElo, "NONE") == 0 || strcmp(lichessElo, "") == 0) {
    tft.printf("Push again to launch seek for:\nTime: %s Increment: %s\nColor: %s\nRated: %s\nVariant: standard\n\nPress other key to cancel", lichessTime, lichessIncrement, lichessColor, lichessRated );
  } else {
    tft.printf("Push again to launch seek for:\nTime: %s Increment: %s\nColor: %s\nRated: %s\nVariant: standard\nELO range: %s\nPress other key to cancel", lichessTime, lichessIncrement, lichessColor, lichessRated, lichessElo );
  }

}



void askForLichessConfirmationTakeBackOffer() {

  //Called from the button read code so the semaphore is already taken

  displayLichessConfirmationMsg = true;

  tft.fillRect(0, 60, 240, 120, TFT_BLACK);
  tft.setCursor(0, 83);
  tft.setTextColor(TFT_WHITE);
  tft.println(" Press again to ask takeback");
  tft.println("");
  tft.println(" Push any other button to abort");

}



void announceHoldMode() {

  //Called from the button read code so the semaphore is already taken

  displayLichessConfirmationMsg = true;

  tft.fillRect(0, 60, 240, 120, TFT_BLACK);
  tft.setCursor(0, 83);
  tft.setTextColor(TFT_WHITE);
  tft.println(" HOLD MODE");
  tft.println(" You can unplug the module");
  tft.println(" or turn it off safely");
  tft.println(" Push any key to release");


}


void announceLoadingResources() {


  tft.fillRect(0, 60, 320, 120, TFT_BLACK);
  tft.setCursor(0, 83);
  tft.setTextColor(TFT_WHITE);
  tft.setTextSize(2);
  tft.println(" UPDATING RESOURCES");
  tft.println(" Please do not turn off");
  tft.println(" the module. It can take");
  tft.println(" up to a minute");

}



void askForLichessConfirmationDrawOffer() {

  //Called from the button read code so the semaphore is already taken

  displayLichessConfirmationMsg = true;

  tft.fillRect(0, 60, 240, 120, TFT_BLACK);
  tft.setCursor(0, 83);
  tft.setTextColor(TFT_WHITE);
  tft.println(" Press again to offer draw");
  tft.println("");
  tft.println(" Push any other button to abort");

}

void askForLichessConfirmationResign() {

  //Called from the button read code so the semaphore is already taken

  displayLichessConfirmationMsg = true;

  tft.fillRect(0, 60, 240, 120, TFT_BLACK);
  tft.setCursor(0, 83);
  tft.setTextColor(TFT_WHITE);
  tft.println(" Press again to resign");
  tft.println("");
  tft.println(" Push any other button to abort");


}


void askForLichessConfirmationOpponentDrawOffer() {

  xSemaphoreTake( xScreenSemaphore, ( TickType_t ) screenSemaphoreTimeout );

  displayLichessConfirmationMsg = true;

  tft.fillRect(0, 60, 240, 120, TFT_BLACK);
  tft.setCursor(0, 83);
  tft.setTextColor(TFT_WHITE);
  tft.println(" Opponent offered a draw");
  tft.println("");
  tft.println(" Push first button to accept");
  tft.println("");
  tft.println(" Any other to decline");
  xSemaphoreGive( ( xScreenSemaphore ) );

}


void askForLichessConfirmationOpponentTakebackProposal() {

  xSemaphoreTake( xScreenSemaphore, ( TickType_t ) screenSemaphoreTimeout );

  displayLichessConfirmationMsg = true;

  tft.fillRect(0, 60, 240, 120, TFT_BLACK);
  tft.setCursor(0, 83);
  tft.setTextColor(TFT_WHITE);
  tft.println(" Opponent ask taking back");
  tft.println("");
  tft.println(" Push first button to accept");
  tft.println("");
  tft.println(" Any other to decline");

  xSemaphoreGive( ( xScreenSemaphore ) );
}




void cancelLichessConfirmation() {
  if (displayLichessConfirmationMsg) {
    displayLichessConfirmationMsg = false;
    memset(lastDrawn, 255, 64);
    memset(lastDrawnBG, 255, 64);
  }


}

void cancelLichessSeekScreen() {
  displayLichessSeekMsg = false;
  memset(lastDrawn, 255, 64);
  memset(lastDrawnBG, 255, 64);

}

void showLichessSeekScreen() {

  //Called from the button read code so the semaphore is already taken

  displayLichessSeekMsg = true;
  tft.fillRect(0, 60, 240, 120, TFT_BLACK);
  tft.setCursor(15, 90);
  tft.setTextColor(TFT_WHITE);
  tft.printf("Searching for an opponent...");



}



void paintLichessGameEndedDraw() {
  xSemaphoreTake( xScreenSemaphore, ( TickType_t ) screenSemaphoreTimeout );

  tft.fillRect(247, 95, 80, 20, TFT_BLACK);
  tft.setCursor(260, 95);
  tft.setTextColor(TFT_DARKGREY);
  tft.print("1/2");

  tft.fillRect(247, 125, 80, 20, TFT_BLACK);
  tft.setCursor(260, 125);
  tft.setTextColor(TFT_DARKGREY);
  tft.print("1/2");

  if (serialLog) Serial.println("-------------------->GAME ENDED DRAW");

  xSemaphoreGive( ( xScreenSemaphore ) );

}

void paintLichessGameWonBottom() {
  xSemaphoreTake( xScreenSemaphore, ( TickType_t ) screenSemaphoreTimeout );

  tft.fillRect(247, 95, 80, 20, TFT_BLACK);
  tft.setCursor(260, 95);
  tft.setTextColor(TFT_RED);
  tft.print("0");

  tft.fillRect(247, 125, 80, 20, TFT_BLACK);
  tft.setCursor(260, 125);
  tft.setTextColor(TFT_GREEN);
  tft.print("1");

  if (serialLog) Serial.println("-------------------->GAME ENDED BOTTOM");

  xSemaphoreGive( ( xScreenSemaphore ) );

}

void paintLichessGameWonTop() {
  xSemaphoreTake( xScreenSemaphore, ( TickType_t ) screenSemaphoreTimeout );

  tft.fillRect(247, 95, 80, 20, TFT_BLACK);
  tft.setCursor(260, 95);
  tft.setTextColor(TFT_GREEN);
  tft.print("1");

  tft.fillRect(247, 125, 80, 20, TFT_BLACK);
  tft.setCursor(260, 125);
  tft.setTextColor(TFT_RED);
  tft.print("0");

  if (serialLog) Serial.println("-------------------->GAME ENDED TOP");

  xSemaphoreGive( ( xScreenSemaphore ) );

}


void onBLEConnectedIcon() {
  if (serialLog) Serial.println("toggle doPaintBLEConnectedIcon");
  doPaintBLEConnectedIcon = true;
  return;
}

void onBLEConnectedIconDisabled() {
  if (serialLog) Serial.println("toggle doPaintBLEConnectedIconDisabled");
  doPaintBLEConnectedIconDisabled = true;
  return;
}


void offBLEConnectedIcon() {
  if (serialLog) Serial.println("toggle doClearBLEConnectedIcon");
  doClearBLEConnectedIcon = true;
  return;
}


void onChess960ModeIcon() {
  if (serialLog) Serial.println("toggle doPaintChess960ModeIcon");
  doPaintChess960ModeIcon = true;
  return;
}


void offChess960ModeIcon() {
  if (serialLog) Serial.println("toggle doClearChess960ModeIcon");
  doClearChess960ModeIcon = true;
  return;
}
